chriscannon9001/OptoSCAD/hw.scad

// Easily inherit all the hardware tools
// include <OptoSCAD/hw.scad>

use <./hwlookup.scad>
use <./hw_pockets.scad>
use <./hw_features.scad>
